Sanjana-Dissanayaka/multimodal-gesture-based-teleoperation-robotic-manipulator/S568d170406594333bfd9a4a69376fcc4k.jpg_720x720q80.jpg_.webp

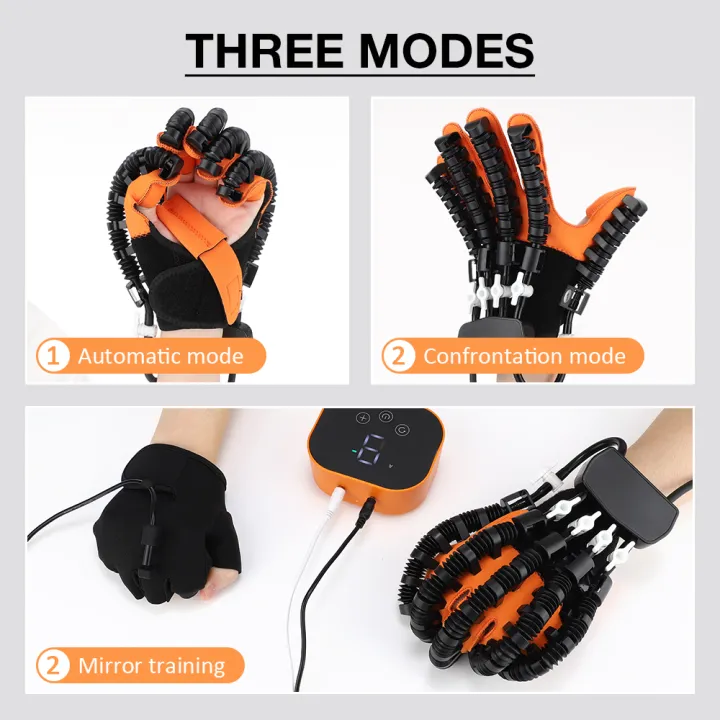
S568d170406594333bfd9a4a69376fcc4k.jpg_720x720q80.jpg_.webp
