Sanjana-Dissanayaka/multimodal-gesture-based-teleoperation-robotic-manipulator/FLEX_TEST/flex1_A1.png

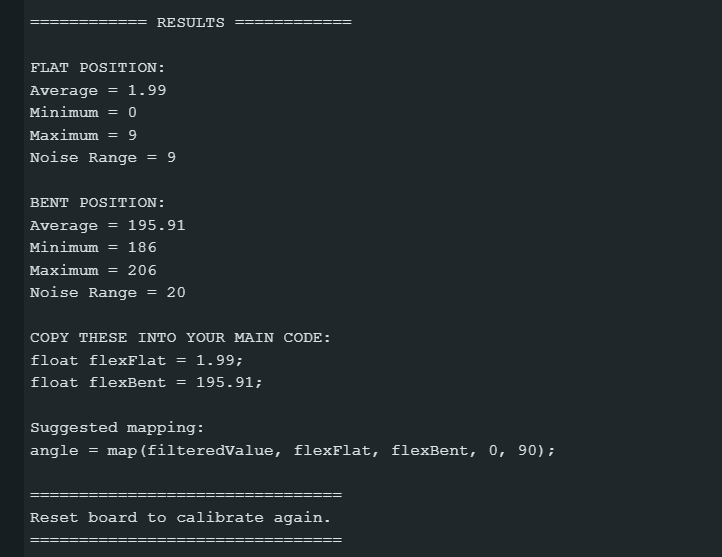
FLEX_TEST/flex1_A1.png
