Sanjana-Dissanayaka/multimodal-gesture-based-teleoperation-robotic-manipulator/FLEX_TEST/flex2_A2.png

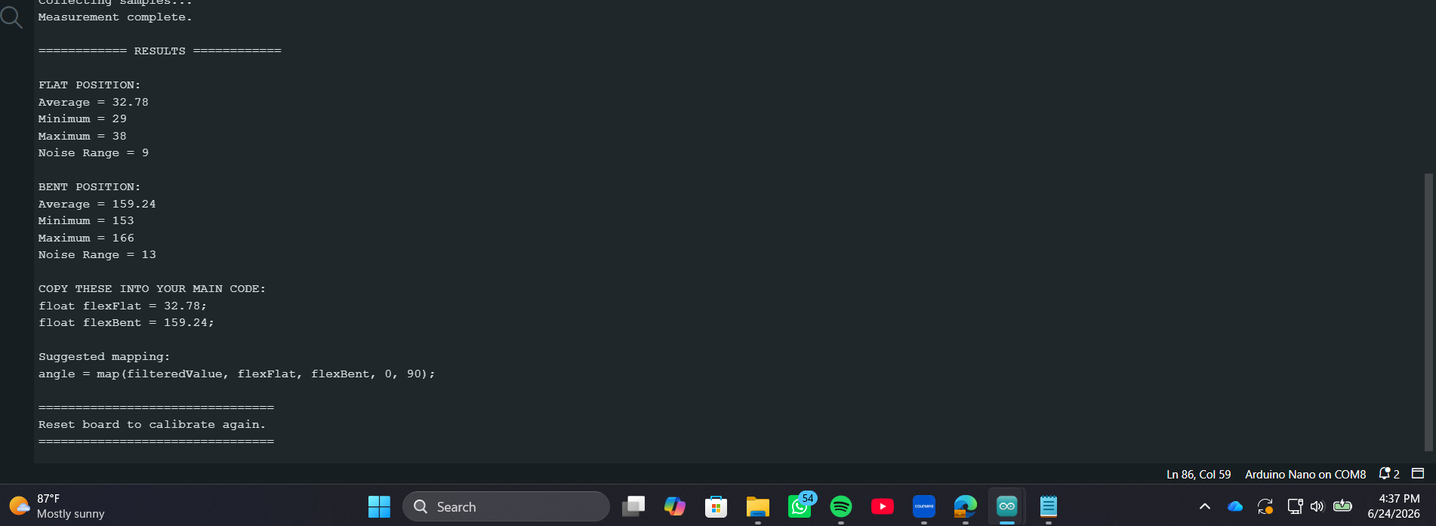
FLEX_TEST/flex2_A2.png
