Sanjana-Dissanayaka/multimodal-gesture-based-teleoperation-robotic-manipulator/FLEX_TEST/flex4_A6.png

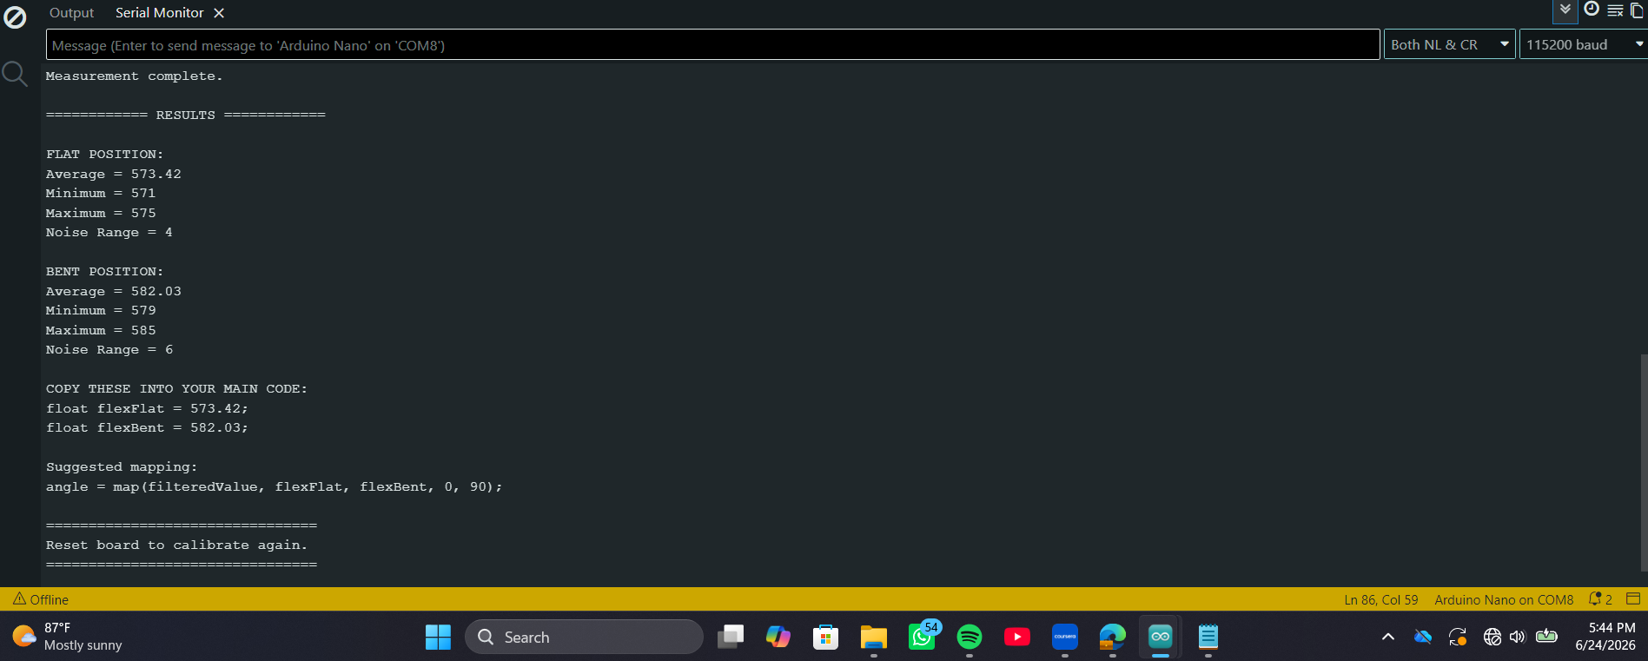
FLEX_TEST/flex4_A6.png
