Sanjana-Dissanayaka/multimodal-gesture-based-teleoperation-robotic-manipulator/MPU6050_TEST/Screenshot 2026-06-16 140601.png

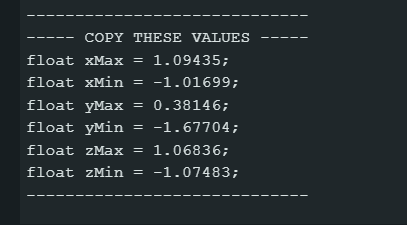
MPU6050_TEST/Screenshot 2026-06-16 140601.png
