Sanjana-Dissanayaka/multimodal-gesture-based-teleoperation-robotic-manipulator/OLED_TEST.png

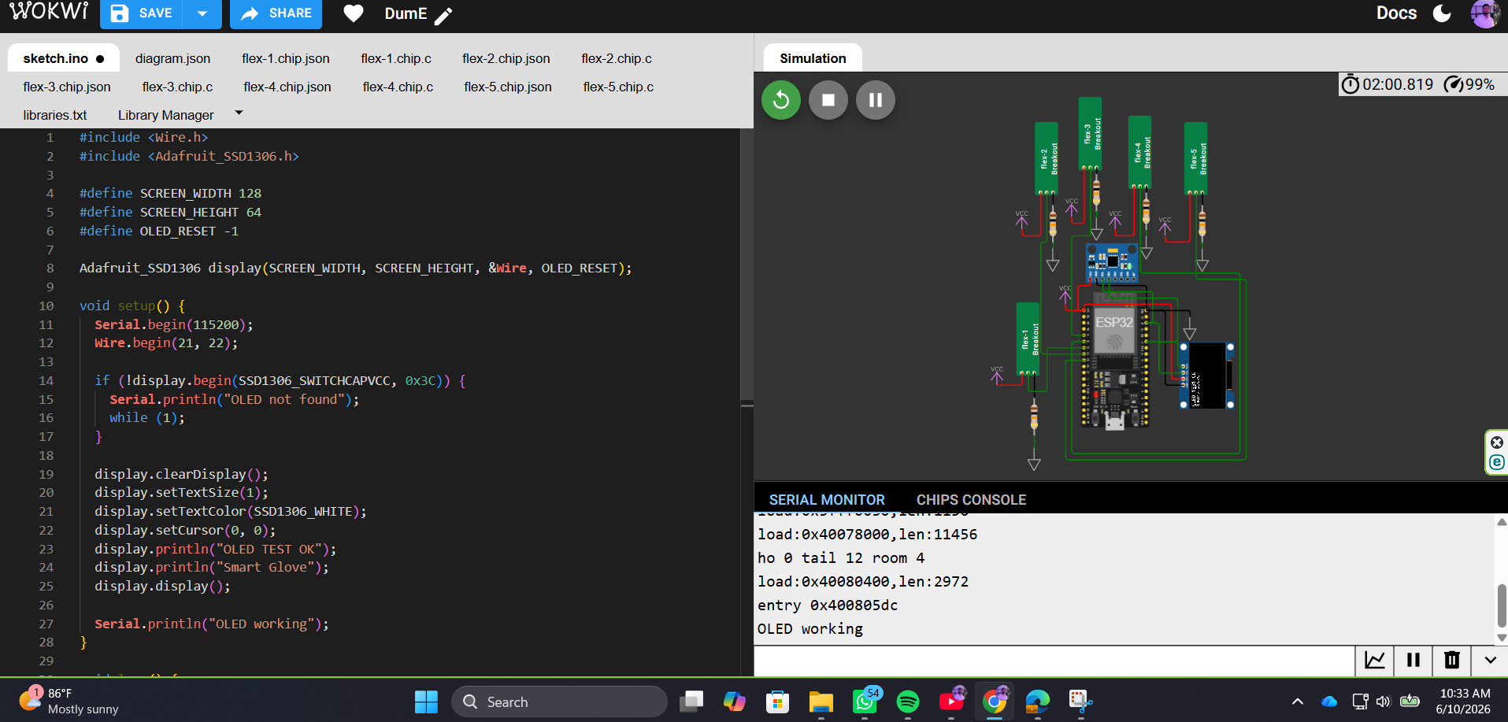
OLED_TEST.png
